Andreas-Wahl/Startlight-3D/#JPEG/Startlight-Baerenkeller_01_3D-View_vorne.jpeg

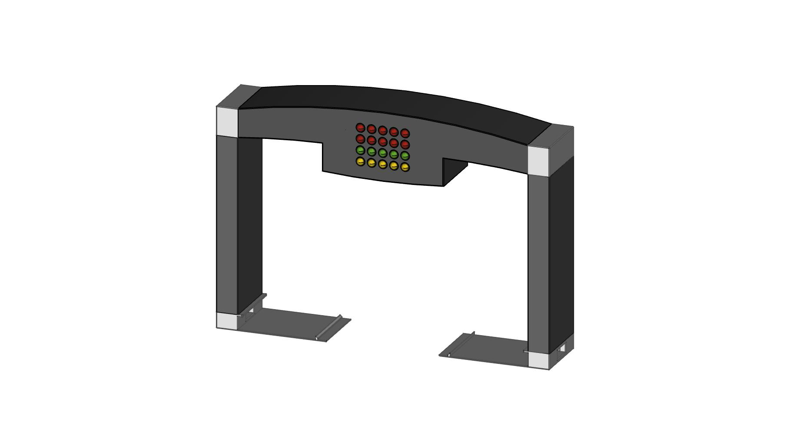
#JPEG/Startlight-Baerenkeller_01_3D-View_vorne.jpeg
