Andreas-Wahl/Startlight-3D/#JPEG/Startlight-Baerenkeller_10_Bruecke.jpeg

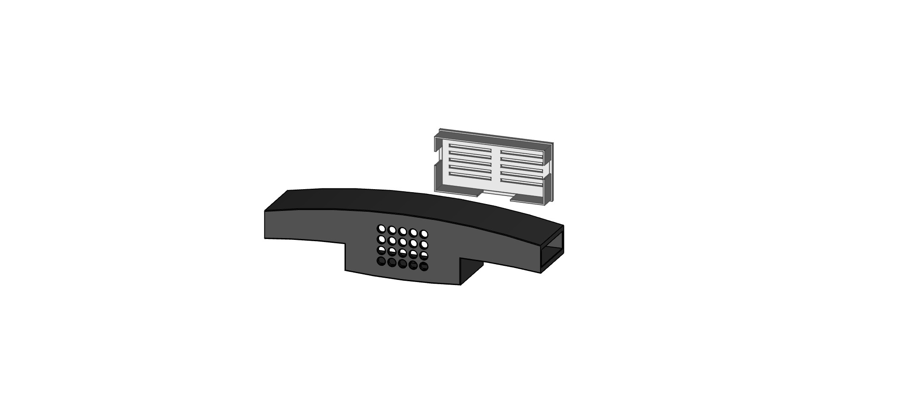
#JPEG/Startlight-Baerenkeller_10_Bruecke.jpeg
