Andreas-Wahl/Startlight-3D/#JPEG/Startlight-Baerenkeller_12_Bruecke_Deckel.jpeg

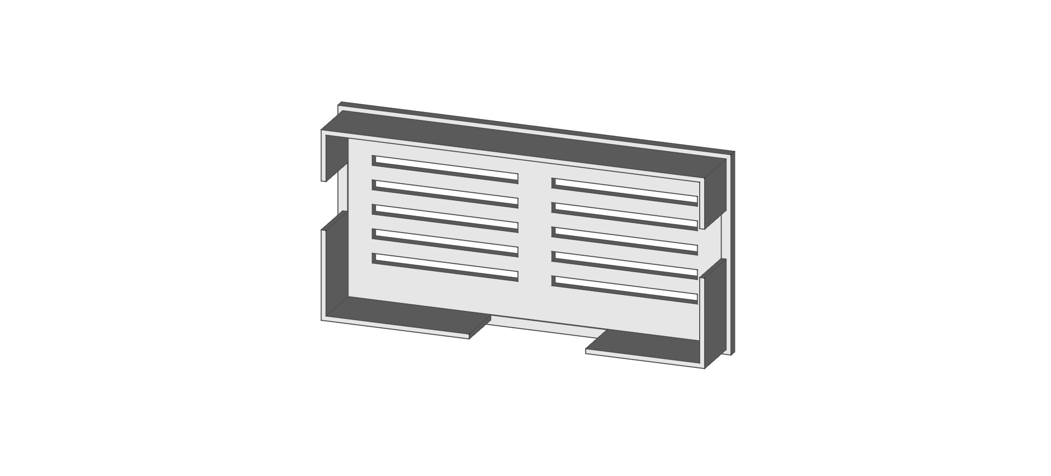
#JPEG/Startlight-Baerenkeller_12_Bruecke_Deckel.jpeg
