Andreas-Wahl/Startlight-3D/#JPEG/Startlight-Baerenkeller_41_Fuesse_Standard.jpeg

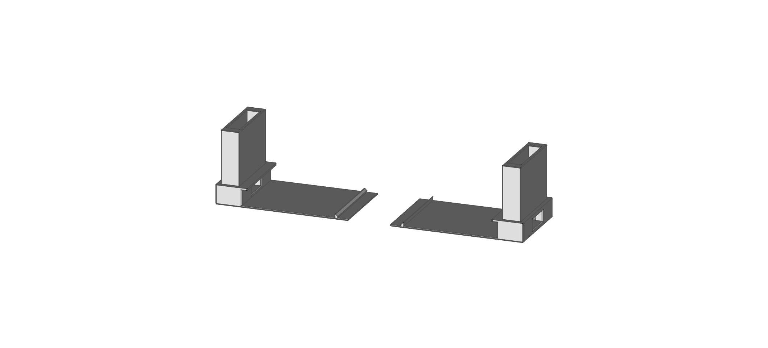
#JPEG/Startlight-Baerenkeller_41_Fuesse_Standard.jpeg
