Andreas-Wahl/Startlight-3D/#JPEG/Startlight-Baerenkeller_42_Fuesse_CU.jpeg

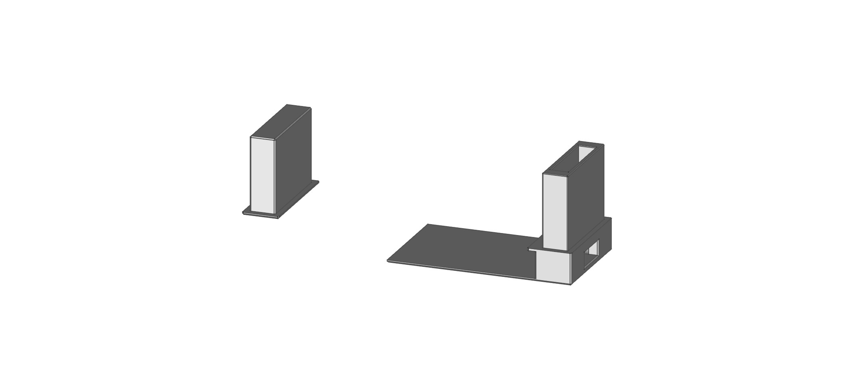
#JPEG/Startlight-Baerenkeller_42_Fuesse_CU.jpeg
