Andreas-Wahl/Startlight-3D/#JPEG/Startlight-Baerenkeller_61_Stecker.jpeg

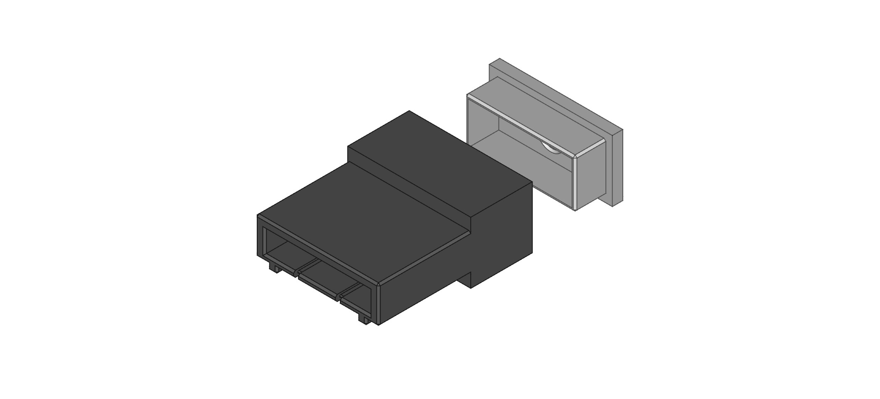
#JPEG/Startlight-Baerenkeller_61_Stecker.jpeg
